MayurRabadiya/Home-Automation-System/4.1/4.1_POWER/pictures/3_light_1_fan.png

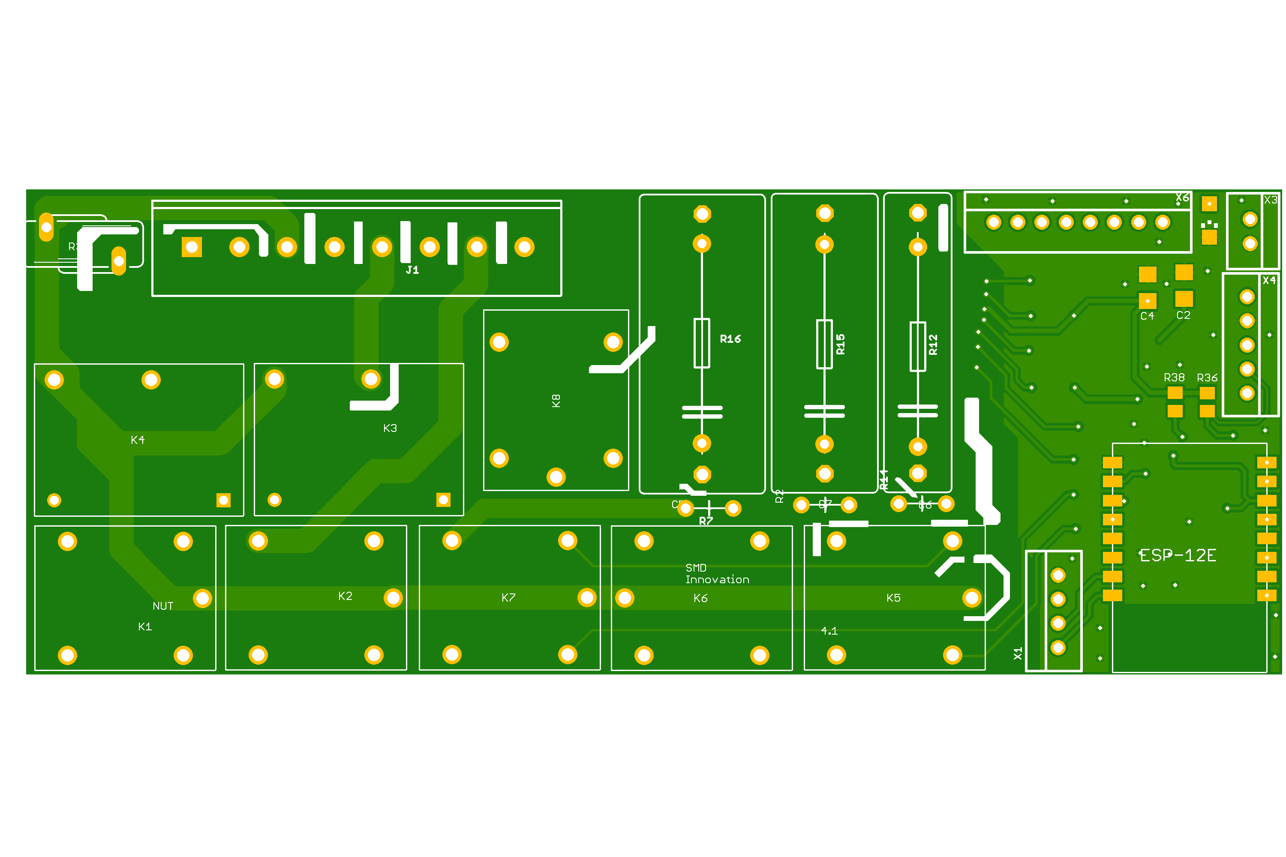
4.1/4.1_POWER/pictures/3_light_1_fan.png
