MayurRabadiya/Home-Automation-System/4.1/4.1_POWER/pictures/123.png

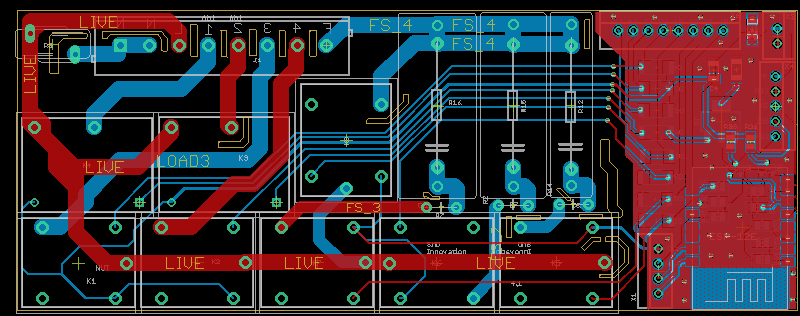
4.1/4.1_POWER/pictures/123.png
