MayurRabadiya/Home-Automation-System/4.1/4.1_TOUCH/pictures/4.1_bot.png

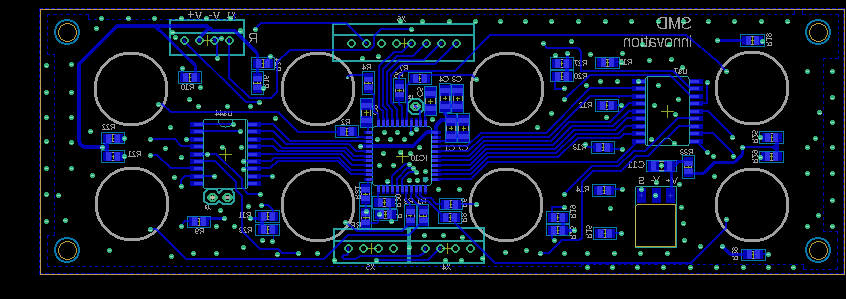
4.1/4.1_TOUCH/pictures/4.1_bot.png
