MayurRabadiya/Home-Automation-System/7.0/7.0_POWER/pictures/6_light_1_fan_base_1.png

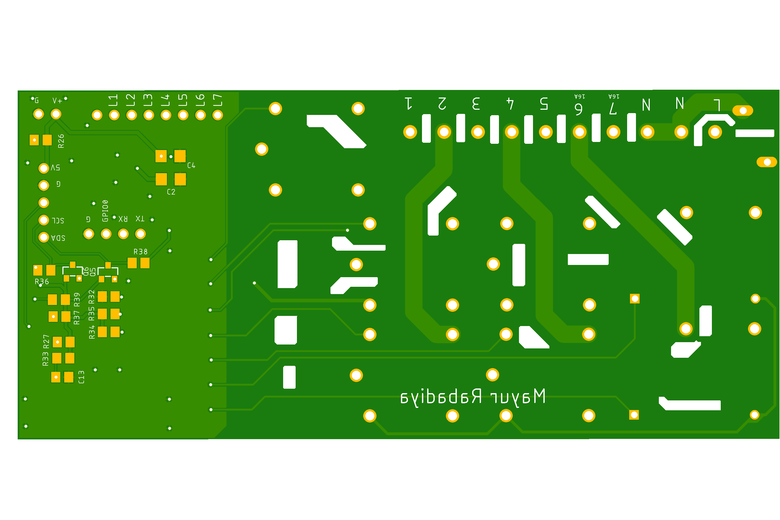
7.0/7.0_POWER/pictures/6_light_1_fan_base_1.png
