MayurRabadiya/Home-Automation-System/7.0/7.0_POWER/pictures/High Power PCB.png

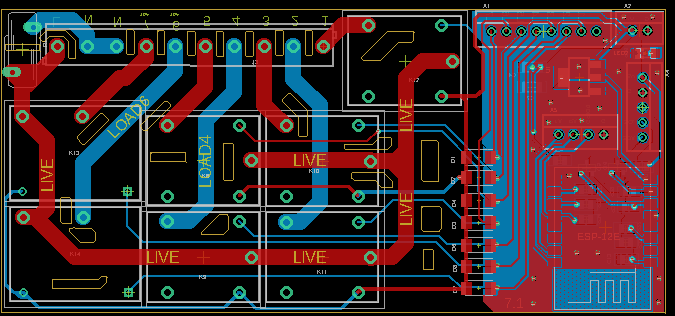
7.0/7.0_POWER/pictures/High Power PCB.png
