MayurRabadiya/Home-Automation-System/7.0/7.0_TOUCH/pictures/6_light_1_fan.png

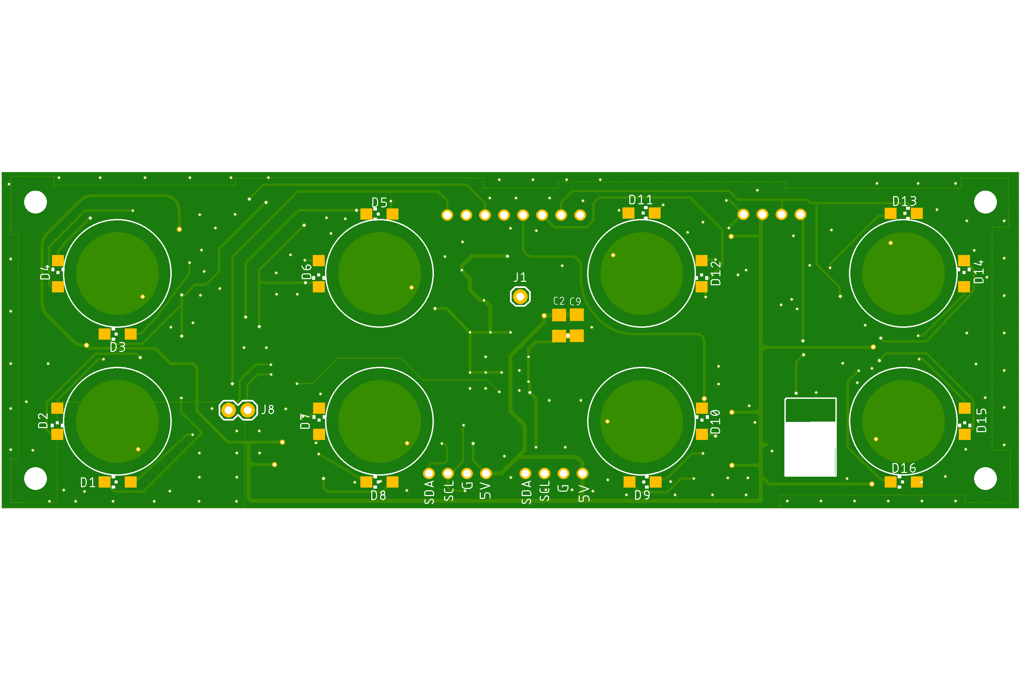
7.0/7.0_TOUCH/pictures/6_light_1_fan.png
