MayurRabadiya/Home-Automation-System/7.0/7.0_TOUCH/pictures/7.png

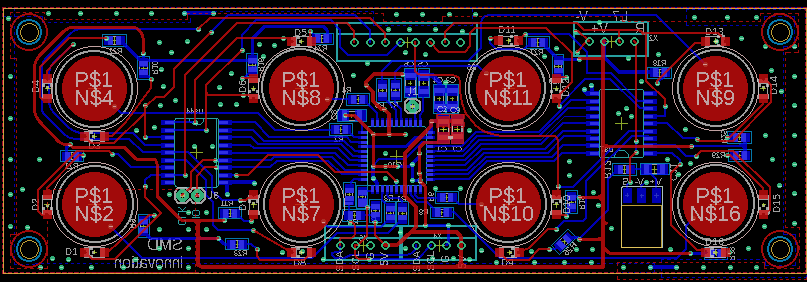
7.0/7.0_TOUCH/pictures/7.png
